Robin-DUBREUIL/opengate/PCB/TopSilkLayer.pdf

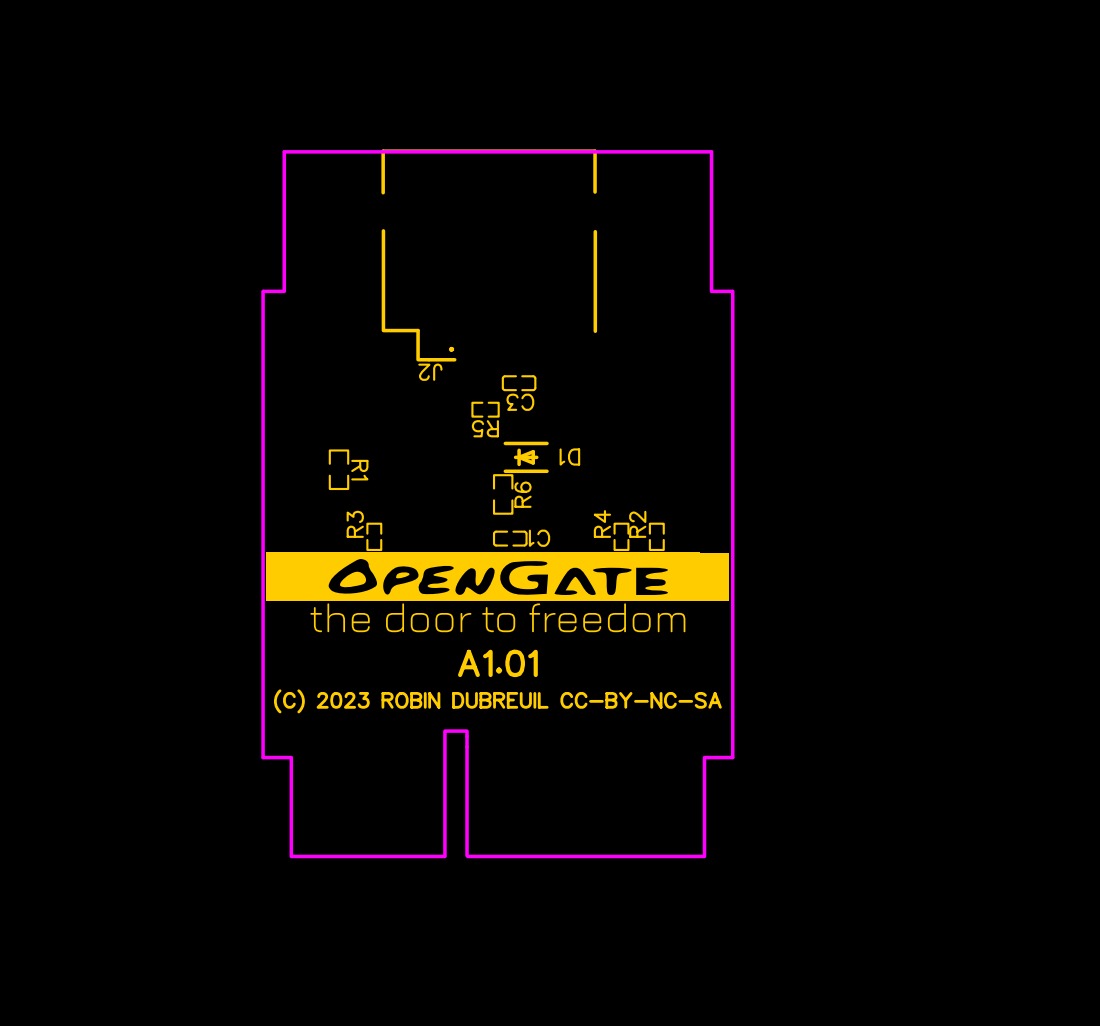
[picture p10: page 1]
